ageppert/Core64/Firmware-PlatformIO/Core64/src/Mode_Manager.h

/*
PURPOSE: 
SETUP:
*/
#ifndef MODE_MANAGER_H
    #define MODE_MANAGER_H
    #include <stdint.h>

    // All of these items in the Enum list must be updated in the corresponding TOP_LEVEL_MODE_NAME_ARRAY of Mode_Manager.cpp to match 1:1.
    enum TopLevelMode                  // Top Level Mode State Machine
    {
    MODE_START_POWER_ON                             ,                        // Start-up, then go to DEMO first demo default
        MODE_START_ALIVE                            ,                        // 
        MODE_START_EEPROM                           ,                        // 
        MODE_START_POWER_CHECK                      ,                        //
        MODE_START_CONFIG_SPECIFIC                  ,                        // 
        MODE_START_SEQUENCE_COMPLETE                ,                        // 
    MODE_DGAUSS_MENU                                ,                        // DGAUSS MENU (TOP LEVEL MENU)
        MODE_DEMO_SUB_MENU                          ,                  // 
            MODE_DEMO_SCROLLING_TEXT                ,             // Scrolling text
            MODE_DEMO_LED_TEST_ONE_MATRIX_MONO      ,             // Testing LED Driver with matrix array and monochrome color
            MODE_DEMO_LED_TEST_ONE_MATRIX_COLOR     ,             // Testing LED Driver with matrix array and multi-color symbols
            //MODE_DEMO_LOW_POWER                   ,             // TODO: Lower power mode
            //MODE_DEMO_SLEEP                       ,             // TODO: Sleep mode 
            MODE_DEMO_END_OF_LIST                   ,             // End of the demo loop, go back to the beginning.
        MODE_GAME_SUB_MENU                          ,                  // 
            MODE_GAME_SNAKE                         ,                  // 
            MODE_GAME_PONG                          ,                  // 
            MODE_GAME_END_OF_LIST                   ,             // End of the game list, go back to the beginning.
        MODE_APP_SUB_MENU                           ,                    // 
            MODE_APP_PAINT                          ,                  // Drawing mode, of course!
            MODE_APP_MIDI                           ,                  // Optional MIDI SAO support
            MODE_APP_END_OF_LIST                    ,              // End of the app list, go back to the beginning.
        MODE_UTIL_SUB_MENU                          ,                  // 
            MODE_UTIL_FLUX_DETECTOR                 ,                  // Flux detector, shows cores being affected by magnetic flux in real-time
            //MODE_UTIL_64BIT_MEMORY                ,                  // TODO: read/write 64 bit values from serial port
            MODE_UTIL_END_OF_LIST                   ,              // End of the util list, go back to the beginning.
        MODE_SPECIAL_SUB_MENU                       ,                  // 
            MODE_SPECIAL_TEST_ONE_CORE              ,                  // 
            MODE_SPECIAL_GLAMOR_SHOT                ,                  // Display a static image for photo shoot
            MODE_LED_TEST_ALL_BINARY                ,                  // Test LED Driver with binary values
            MODE_LED_TEST_ONE_STRING                ,                  // Testing LED Driver
            MODE_TEST_EEPROM                        ,                  // Read out the raw EEPROM values
            MODE_LED_TEST_ALL_COLOR                 ,                  // Test LED Driver with all pixels and all colors
            MODE_CORE_TOGGLE_BITS_WITH_3V3_READ     ,                  // Test one core with one function
            MODE_CORE_TEST_ONE                      ,                  // Testing core #coreToTest and displaying core state
            MODE_CORE_TEST_MANY                     ,                  // Testing multiple cores and displaying core state
            MODE_HALL_TEST                          ,                  // Testing hall switch and sensor response
            MODE_LED_TEST_ALL_RGB                   ,                  // Test all LEDs through R G B White 
            MODE_GPIO_TEST                          ,                  // Testing all GPIO outputs
            //MODE_SPECIAL_STANDALONE_TEST          ,                  // TODO: For the manufacturing test fixture, test unused IO pins
            MODE_SPECIAL_LOOPBACK_TEST              ,                  // For the manufacturing test fixture, test unused IO pins
            MODE_SPECIAL_HARD_REBOOT                ,                  // Hard Reboot.
            MODE_SPECIAL_END_OF_LIST                ,              // End of the special list, go back to the beginning.
        MODE_SETTINGS_SUB_MENU                      ,                  // TODO: Implement sub-menu
            //MODE_SETTINGS_BRIGHTNESS              ,                  // TODO: Adjust screen brightness, and select automatic adjustment on/off
            //MODE_SETTINGS_EEPROM_USER_SETTINGS    ,                  // TODO:
            //MODE_SETTINGS_EEPROM_USER_NAME        ,                  // TODO:
            MODE_SETTINGS_END_OF_LIST               ,              // End of the settings list, go back to the beginning.
    MODE_MANUFACTURING_MENU                         ,                  // TODO: Implement sub-menu. Only accessible from the command line. Not accessible from DGAUSS menu.
        MODE_MANUFACTURING_EEPROM_FACTORY_WRITE     ,                  // Write EEPROM with pre-formatted string during manufacturing process. 
        MODE_MANUFACTURING_END_OF_LIST              ,              // End of the manufacturing list, go back to the beginning.
    MODE_LAST                                                        // Last one, return to Startup 0. Note, this is different than "default" which is handled by switch/case statement.
    } ;

    extern const char* TOP_LEVEL_MODE_NAME_ARRAY[];

    void TopLevelModeManagerCheckButtons ();

    void TopLevelModeDefaultSet     (uint16_t value);
    uint16_t TopLevelModeDefaultGet ();

    void    TopLevelModeSetToDefault();

    void    TopLevelModeSet          (uint16_t value);
    void    TopLevelModeSetInc       ();
    void    TopLevelModeSetDec       ();
    uint16_t TopLevelModeGet         ();

    void TopLevelModePreviousSet     (uint16_t value);
    uint16_t TopLevelModePreviousGet ();

    void    TopLevelModeSetChanged   (bool value);
    bool    TopLevelModeChangedGet   ();

    void TopLevelThreeSoftButtonGlobalEnableSet (bool value);
    bool TopLevelThreeSoftButtonGlobalEnableGet ();

    void TopLevelSetMenuButtonGlobalEnableSet (bool value);
    bool TopLevelSetMenuButtonGlobalEnableGet ();

    void TopLevelSetSoftButtonGlobalEnableSet (bool value);
    bool TopLevelSetSoftButtonGlobalEnableSet ();

    void    TopLevelModeManagerRun   ();

    void MenuTimeOutCheckReset ();
    bool MenuTimeOutCheck (uint32_t MenuTimeoutLimitms);

    void    CoreToStartTestSet (uint8_t value);
    uint8_t CoreToStartTestGet              ();
    void    CoreToEndTestSet   (uint8_t value);
    uint8_t CoreToEndTestGet                ();

#endif // MODE_MANAGER_H
