ageppert/Core64/Firmware-PlatformIO/Core64/src/APPS/App_Midi.h

/*
PURPOSE: If MIDI SAO is connected and enabled in hardware settings, output state of core memory to MIDI notes.
SETUP:
*/
 
#ifndef APP_MIDI_H
    #define APP_MIDI_H

    #include <stdint.h>

    void AppMidi();

#endif // APP_MIDI_H
