ageppert/Core64/Firmware-PlatformIO/Core64/src/SubSystems/Heart_Beat.cpp

#include <stdint.h>
#include <stdbool.h>

//#if (ARDUINO >= 100)
#include <Arduino.h>          // Not sure why, but this is required for Arduino IDE to recognize OUTPUT in the pinMode of setup.
//#else
//#include <WProgram.h>
//#endif

#include "SubSystems/Heart_Beat.h"
#include "Config/HardwareIOMap.h"

void HeartBeatSetup() {
  pinMode(Pin_Built_In_LED, OUTPUT);
  #if defined  MCU_TYPE_MK20DX256_TEENSY_32
    #ifdef NEON_PIXEL_ARRAY
      // Don't perform a heart beat because it will mess up the Neon Pixels since the Heart Beat LED is shared with the SPI CLK pin.
    #else
      digitalWriteFast(Pin_Built_In_LED, 1);
    #endif
  #elif defined MCU_TYPE_RP2040
    digitalWrite(Pin_Built_In_LED, 1);
  #endif
}

// Purpose: Blink an LED so the user knows the system is alive.
void HeartBeat() {
  static unsigned long HeartBeatSequence[] = {150,150,150,550}; // On, off, on, off 
  static unsigned HeartBeatSequencePosition = 0;
  static unsigned long NowTime = 0;
  static uint8_t LED_HEARTBEAT_STATE = 1;
  static unsigned long ledHeartBeatTimer = 0;
  NowTime = millis();
  if ((NowTime - ledHeartBeatTimer) >= HeartBeatSequence[HeartBeatSequencePosition])
  {
    LED_HEARTBEAT_STATE = !LED_HEARTBEAT_STATE;
    ledHeartBeatTimer = NowTime;
    HeartBeatSequencePosition++;
    if(HeartBeatSequencePosition>3) {HeartBeatSequencePosition = 0;}
  }
  #if defined  MCU_TYPE_MK20DX256_TEENSY_32
    digitalWriteFast(Pin_Built_In_LED, LED_HEARTBEAT_STATE);
  #elif defined MCU_TYPE_RP2040
    if (PicoWPresent) { 
      // cyw43_arch_gpio_put(CYW43_WL_GPIO_LED_PIN, LED_HEARTBEAT_STATE);   
      digitalWrite(LED_BUILTIN, LED_HEARTBEAT_STATE);
    }
    else { 
      digitalWrite(Pin_Built_In_LED, LED_HEARTBEAT_STATE); 
      }
  #endif
}
